MuteSpirit/CredsHolder/poc/ui-mpu-6050-with-oled-on-arduino-uno/Arduino-MPU_OLED_bb.jpg

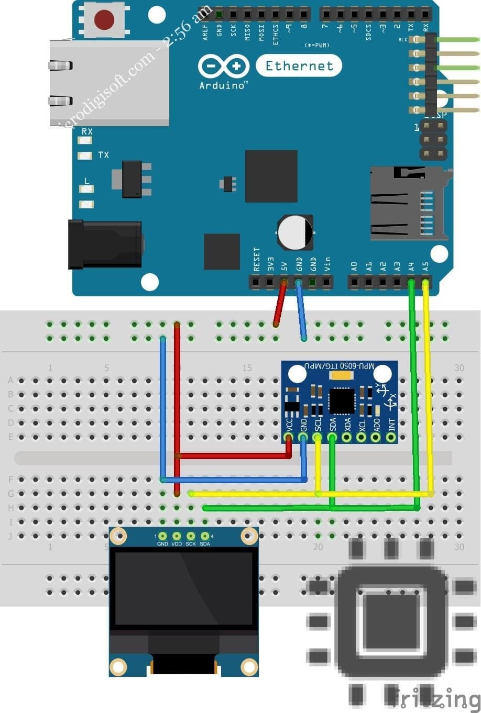
poc/ui-mpu-6050-with-oled-on-arduino-uno/Arduino-MPU_OLED_bb.jpg
