MuteSpirit/CredsHolder/proposals/creds-holder-navigation-option1-proposals-chevron-on-place.png

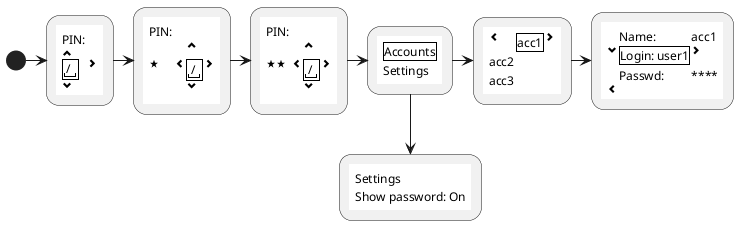
proposals/creds-holder-navigation-option1-proposals-chevron-on-place.png
