MuteSpirit/CredsHolder/src/device.cpp

// CredsHolder (Hardware Credential Manager)
// Copyright (C)  2026  Ivan Efimov aka MuteSpirit <mutespirit@yandex.ru>.
//
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
// You should have received a copy of the GNU General Public License
// along with this program.  If not, see <https://www.gnu.org/licenses/>.
#include "creds_holder.hpp"

#include <new>
#include <math.h>

#include <Arduino.h>

// Arduino Wire library is required if I2Cdev I2CDEV_ARDUINO_WIRE implementation
// is used in I2Cdev.h
#if I2CDEV_IMPLEMENTATION == I2CDEV_ARDUINO_WIRE
    #include "Wire.h"
#endif

// To be able handle MPU6050 events in time and avoid chip FIFO overloading
// it's needed to decrease speed of evetns generation to acceptable level
#define MPU6050_DMP_FIFO_RATE_DIVISOR 64 // work enough stable
// #define MPU6050_DMP_FIFO_RATE_DIVISOR 0x10 // ~ 60 Hz

#include "MPU6050/I2Cdev.h"
#include "MPU6050/MPU6050_6Axis_MotionApps20.h"
// TODO: try newer firmware from
// #include "MPU6050/MPU6050_6Axis_MotionApps612.h"
#include "MPU6050/MPU6050.h"

#include "device.hpp"

////////////////////////////////////////////////////////////////////////////////
enum class Movement : uint8_t
{
    clockwise,
    ccw, // counterclockwise
    none
};

struct SplashDetectCtx
{
    float ema {0.0f}; /// Exponential moving average

    /// like for keyboard we must detect when splash dissapear
    /// to react "not on button push but pull"
    uint8_t splashStarted {0};

    Movement mv {Movement::none};
};

class CredsHolderInputsImpl
{
public:
    CredsHolderInputsImpl(DeviceOutputs&);

public:
    DeviceOutputs& deviceOutputs_;

    BlindCall hooks_[static_cast<uint8_t>(DeviceInputs::UserAction::size)];

    MPU6050 mpu_;
    uint16_t packetSize_;    // expected DMP packet size (default is 42 bytes)
    uint8_t fifoBuffer_[64]; // FIFO storage buffer
                             //
    SplashDetectCtx pitchDetectCtx_;
    SplashDetectCtx rollDetectCtx_;
};

static volatile bool mpuInterrupt {false}; // indicates whether MPU interrupt pin has gone high
void dmpDataReady() {
    mpuInterrupt = true;
}

CredsHolderInputsImpl::CredsHolderInputsImpl(DeviceOutputs& deviceOutputs)
    : deviceOutputs_(deviceOutputs)
{
    for (size_t i = 0; i < static_cast<uint8_t>(DeviceInputs::UserAction::size); ++i) {
        hooks_[i] = BlindCall::stub();
    }
}

////////////////////////////////////////////////////////////////////////////////
CredsHolderInputs::CredsHolderInputs(DeviceOutputs& deviceOutputs)
{
    static_assert(sizeof(impl_) == sizeof(CredsHolderInputsImpl), "fix CredsHolderInputs::impl_ size");
    new(impl_) CredsHolderInputsImpl(deviceOutputs);
}

CredsHolderInputsImpl* CredsHolderInputs::impl()
{
    return reinterpret_cast<CredsHolderInputsImpl*>(impl_);
}

void
CredsHolderInputs::set(UserAction act, BlindCall cb)
{
    impl()->hooks_[static_cast<uint8_t>(act)] = cb;
}

void
CredsHolderInputs::unset(UserAction act)
{
    impl()->hooks_[static_cast<uint8_t>(act)] = BlindCall::stub();
}

bool
CredsHolderInputs::setup(void)
{
    // if (Serial) {Serial.println(F("CredsHolderInputs::setup 1"));}
#if I2CDEV_IMPLEMENTATION == I2CDEV_ARDUINO_WIRE
    Wire.begin();
    Wire.setClock(400000); // 400kHz I2C clock. Comment this line if having compilation difficulties
#elif I2CDEV_IMPLEMENTATION == I2CDEV_BUILTIN_FASTWIRE
    Fastwire::setup(400, true);
#endif

    MPU6050* mpu = &impl()->mpu_;

    mpu->initialize();

    // if (Serial) {Serial.println(F("CredsHolderInputs::setup 2"));}

    uint8_t devStatus = mpu->dmpInitialize(/* rate */ 20);
    if (devStatus != 0) {
        return false;
    }

    // if (Serial) {Serial.println(F("CredsHolderInputs::setup 3"));}

    // TODO: make initial calibration, store init values in internal memory and reuse when they are present
    // for my concrete MPU6050 module next offsets has been detected during calibration:
    mpu->setXAccelOffset(2508);
    mpu->setYAccelOffset(-2151);
    mpu->setZAccelOffset(992);

    mpu->setXGyroOffset(-147);
    mpu->setYGyroOffset(25);
    mpu->setZGyroOffset(68); 

    // Calibration Time: generate offsets and calibrate our MPU6050
    // mpu->CalibrateAccel(6);
    // mpu->CalibrateGyro(6);

    // if (Serial) {Serial.println(F("CredsHolderInputs::setup 4"));}

    // turn on the DMP, now that it's ready
    mpu->setDMPEnabled(true);

    // if (Serial) {Serial.println(F("CredsHolderInputs::setup 5"));}

    // enable Arduino interrupt detection
    attachInterrupt(digitalPinToInterrupt(MPU6050_CS_PIN), dmpDataReady, RISING);

    // TODO: add interrupts handling
    // uint8_t mpuIntStatus = mpu->getIntStatus();

    // set our DMP Ready flag so the main loop() function knows it's okay to use it

    // get expected DMP packet size for later comparison
    impl()->packetSize_ = mpu->dmpGetFIFOPacketSize();

    return true;
}

static bool isTiltHappen(SplashDetectCtx &ctx, const float p);

void
CredsHolderInputs::loop_step(void)
{
    // bool nothingToDo = true;
    //
    // noInterrupts();
    // if (mpuInterrupt) {
    //     mpuInterrupt = false;
    //     nothingToDo = false;
    // }
    // interrupts();
    //
    // if (nothingToDo) {
    //     return;
    // }

    if (!impl()->mpu_.dmpGetCurrentFIFOPacket(impl()->fifoBuffer_)) { // Get the Latest packet }
        // if (Serial) { Serial.println(impl()->mpu_.dmpGetFIFOPacketSize()); }
        return;
    }

    VectorFloat gravity;    // [x, y, z]            gravity vector
    Quaternion q;           // [w, x, y, z]         quaternion container
    float ypr[3];           // [yaw, pitch, roll]   yaw/pitch/roll container and gravity vector

    impl()->mpu_.dmpGetQuaternion(&q, impl()->fifoBuffer_);
    impl()->mpu_.dmpGetGravity(&gravity, &q);
    impl()->mpu_.dmpGetYawPitchRoll(ypr, &q, &gravity);

    if (Serial) {
        Serial.print(ypr[1] * 180 / M_PI); 
        Serial.print("; "); 
        Serial.print(ypr[2] * 180 / M_PI); 
        Serial.println(); 
    }

    uint8_t splashStarted = impl()->pitchDetectCtx_.splashStarted;
    if (isTiltHappen(impl()->pitchDetectCtx_, ypr[1] * 180 / M_PI)) {
        if (impl()->pitchDetectCtx_.mv == Movement::clockwise) {
            if (Serial) {Serial.println(F("UserAction::up"));}
            impl()->hooks_[static_cast<uint8_t>(UserAction::up)]();
        } else {
            if (Serial) {Serial.println(F("UserAction::down"));}
            impl()->hooks_[static_cast<uint8_t>(UserAction::down)]();
        }
    } else {
        if (0 == splashStarted && impl()->pitchDetectCtx_.splashStarted > 0) {
            // enough big tilt angle has been detected
            impl()->deviceOutputs_.notify(DeviceOutputs::Feedback::halfTilt);
        } 
    }

    splashStarted = impl()->rollDetectCtx_.splashStarted;
    if (isTiltHappen(impl()->rollDetectCtx_, ypr[2] * 180 / M_PI)) {
        if (impl()->rollDetectCtx_.mv == Movement::clockwise) {
            if (Serial) {Serial.println(F("UserAction::left"));}
            impl()->hooks_[static_cast<uint8_t>(UserAction::left)]();
        } else {
            if (Serial) {Serial.println(F("UserAction::right"));}
            impl()->hooks_[static_cast<uint8_t>(UserAction::right)]();
        }
    } else {
        if (0 == splashStarted && impl()->rollDetectCtx_.splashStarted > 0) {
            // enough big tilt angle has been detected
            impl()->deviceOutputs_.notify(DeviceOutputs::Feedback::halfTilt);
        } 
    }

}

////////////////////////////////////////////////////////////////////////////////
static
bool
isTiltHappen(SplashDetectCtx &ctx, const float p)
{
  constexpr float threshold = 7; // usually tilt angle is about 15 degrees
  constexpr float alpha = 0.15;

  ctx.ema = alpha * p + (1.0 - alpha) * ctx.ema;

  float delta = p - ctx.ema;

  if (abs(delta) >= threshold) {
    ++ctx.splashStarted;
    // FIXME: we may quickly tilt device up and down and "mv" will
    // be updated to the latest tilt accordingly
    ctx.mv = (delta >= 0) ? Movement::clockwise : Movement::ccw;

    if (ctx.splashStarted >= 3) {
      // MPU-6050 DMP is configured to measure 1 time per second
      // so if we see that splash is happening 3 second in a raw
      // then it's just a new position of device
      // TODO: decide how detect "long tilt"
      ctx.splashStarted = 0;
      ctx.mv = Movement::none;
    }
    return false;
  } else {
    if (ctx.splashStarted > 0) {
      // we return device back to original position
      // so tilt finished and device may start a reaction
      ctx.splashStarted = 0;
      return true;
    } else {
      ctx.mv = Movement::none;
      return false;
    }
  }
}

////////////////////////////////////////////////////////////////////////////////
CredsHolderOutputs::CredsHolderOutputs(const uint8_t vibroMotorPin)
: vibroMotorPin_(vibroMotorPin)
{}

bool
CredsHolderOutputs::setup(void)
{
    pinMode(vibroMotorPin_, OUTPUT);
    digitalWrite(vibroMotorPin_, LOW); // to avoid active vibration at device boot time
    return true;
}

void
CredsHolderOutputs::loop_step(void)
{}


void
CredsHolderOutputs::notify(Feedback fb)
{
    switch (fb) {
        case Feedback::halfTilt:
            digitalWrite(vibroMotorPin_, HIGH);
            delay(shortBipDelayMs);
            digitalWrite(vibroMotorPin_, LOW);
            break;

        default:
            break;
    }
}
