MuteSpirit/CredsHolder/src/device.hpp

// CredsHolder (Hardware Credential Manager)
// Copyright (C)  2026  Ivan Efimov aka MuteSpirit <mutespirit@yandex.ru>.
//
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
// You should have received a copy of the GNU General Public License
// along with this program.  If not, see <https://www.gnu.org/licenses/>.
#pragma once

#include "creds_holder.hpp"
#include <Arduino.h>

#include "device_inputs.hpp"
#include "device_outputs.hpp"

#if defined(ARDUINO_ARCH_AVR) // Arduino

// OLED Display
#define OLED_SDA_PIN    2
#define OLED_SCK_PIN    3
#define OLED_I2C_ADDR   0x3C

#define MPU6050_CS_PIN  D5

#define VIBRO_MOTOR_IN_PIN  D10

#elif defined(ARDUINO_ARCH_NRF52) // Pro Micro nRF52840

// OLED Display
#define OLED_SDA_PIN    D6
#define OLED_SCK_PIN    D7
#define OLED_I2C_ADDR   0x3C

#define MPU6050_CS_PIN  D5

#define VIBRO_MOTOR_IN_PIN  D10

#elif defined(EPOXY_DUINO) // Unit tests

// OLED Display
#define OLED_SDA_PIN    D6
#define OLED_SCK_PIN    D7
#define OLED_I2C_ADDR   0x3C

#define MPU6050_CS_PIN  D5

#define VIBRO_MOTOR_IN_PIN  D10

#else
#error("Unknown board type")
#endif // defined(ARDUINO_ARCH_AVR)

class CredsHolderInputsImpl;

////////////////////////////////////////////////////////////////////////////////
class CredsHolderInputs : public DeviceInputs
{
public:
    CredsHolderInputs(DeviceOutputs&);

    virtual void set(UserAction act, BlindCall cb) override;
    virtual void unset(UserAction act) override;

    /// @return "true" if Ok and "false" if initializing fail and device cannot be used, init reboot in that case.
    virtual bool setup(void) override;

    virtual void loop_step(void) override;

protected:
    CredsHolderInputsImpl* impl();

protected:
    uint8_t impl_[296]; /// "insulation' for internal data
};

////////////////////////////////////////////////////////////////////////////////
class CredsHolderOutputs : public DeviceOutputs
{
public:
    CredsHolderOutputs(const uint8_t vibroMotorPin = VIBRO_MOTOR_IN_PIN);

    virtual void notify(Feedback) override;

    virtual bool setup(void) override;
    virtual void loop_step(void) override;

protected:
    uint8_t vibroMotorPin_;
    constexpr static const size_t shortBipDelayMs = 175; // ms
};
