MuteSpirit/CredsHolder/src/accounts_menu.t.cpp

// CredsHolder (Hardware Credential Manager)
// Copyright (C)  2026  Ivan Efimov aka MuteSpirit <mutespirit@yandex.ru>.
//
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
// You should have received a copy of the GNU General Public License
// along with this program.  If not, see <https://www.gnu.org/licenses/>.
#if defined(EPOXY_DUINO)

#include "accounts_menu.hpp"

#include <array>

#include "device_inputs.hpp"
#include "settings.hpp"
#include "memory_block_storage.hpp"

#include "model/account.hpp"
#include "model/storage.hpp"

#include "t/in_memory_oled.hpp"
#include "t/imitated_user_unputs.hpp"

// Must be included as the last one to avoid troubles with macro "test"
// when such word is used in headers above
#include <AUnitVerbose.h>

class AccountsMenuTest : public aunit::TestOnce
{
public:
    virtual void setup() override
    {
        TestOnce::setup();

        memset(buf, 0, sz);
    }

protected:
    OledInMem<16, 4> oled_;
    ImitatedUserInputs userInputs_;
    MemoryBlockStorage<1024, 64> bs_;
    ModelStorage<Account> ms_ {bs_};

    constexpr static uint8_t sz = 16;
    char buf[sz];
};

testF(AccountsMenuTest, ctor)
{
    AccountsMenu menu(oled_, userInputs_, ms_);
};

testF(AccountsMenuTest, draw_empty_account_storage)
{
    AccountsMenu menu(oled_, userInputs_, ms_);

    menu.draw();

    oled_.getLine(0, buf, sz); assertStringCaseEqual("Accounts", buf);
    oled_.getLine(1, buf, sz); assertStringCaseEqual("", buf);
    oled_.getLine(2, buf, sz); assertStringCaseEqual("", buf);
    oled_.getLine(3, buf, sz); assertStringCaseEqual("", buf);
}

testF(AccountsMenuTest, draw_single_account)
{
    Account acc {"acc0", "login", "passwd"};
    assertTrue(ms_.add(acc));

    AccountsMenu menu(oled_, userInputs_, ms_);

    menu.draw();

    oled_.getLine(0, buf, sz); assertStringCaseEqual("Accounts", buf);
    oled_.getLine(1, buf, sz); assertStringCaseEqual("acc0", buf);
    oled_.getLine(2, buf, sz); assertStringCaseEqual("", buf);
    oled_.getLine(3, buf, sz); assertStringCaseEqual("", buf);
}

testF(AccountsMenuTest, draw_the_same_accounts_as_visible)
{
    std::array<Account, 3> aa {{
        {"acc0", "login0", "passwd0"},
        {"acc1", "login1", "passwd1"},
        {"acc2", "login2", "passwd2"},
    }};

    for (auto acc : aa) {
        assertTrue(ms_.add(acc));
    }

    AccountsMenu menu(oled_, userInputs_, ms_);

    assertTrue(aa[0] == menu.selected());

    oled_.clear();
    menu.draw();

    memset(buf, 0, sz);
    oled_.getLine(0, buf, sz); assertStringCaseEqual("Accounts", buf);
    oled_.getLine(1, buf, sz); assertStringCaseEqual("acc0", buf);
    oled_.getLine(2, buf, sz); assertStringCaseEqual("acc1", buf);
    oled_.getLine(3, buf, sz); assertStringCaseEqual("acc2", buf);

    menu.activate();

    userInputs_.tilt(DeviceInputs::UserAction::down); // acc0 ->acc1
    assertTrue(aa[1] == menu.selected());

    userInputs_.tilt(DeviceInputs::UserAction::down); // acc1 ->acc2
    assertTrue(aa[2] == menu.selected());

    userInputs_.tilt(DeviceInputs::UserAction::down); // acc2 ->acc0
    assertTrue(aa[0] == menu.selected());

    oled_.clear();
    menu.draw();

    memset(buf, 0, sz);
    oled_.getLine(0, buf, sz); assertStringCaseEqual("Accounts", buf);
    oled_.getLine(1, buf, sz); assertStringCaseEqual("acc0", buf);
    oled_.getLine(2, buf, sz); assertStringCaseEqual("acc1", buf);
    oled_.getLine(3, buf, sz); assertStringCaseEqual("acc2", buf);
}

testF(AccountsMenuTest, draw_more_accounts_then_visible)
{
    std::array<Account, 4> aa {{
        {"acc0", "login0", "passwd0"},
        {"acc1", "login1", "passwd1"},
        {"acc2", "login2", "passwd2"},
        {"acc3", "login3", "passwd3"}
    }};

    for (auto acc : aa) {
        assertTrue(ms_.add(acc));
    }

    AccountsMenu menu(oled_, userInputs_, ms_);
    menu.activate();

    assertTrue(aa[0] == menu.selected());
    menu.draw();

    oled_.getLine(0, buf, sz); assertStringCaseEqual("Accounts", buf);
    oled_.getLine(1, buf, sz); assertStringCaseEqual("acc0", buf);
    oled_.getLine(2, buf, sz); assertStringCaseEqual("acc1", buf);
    oled_.getLine(3, buf, sz); assertStringCaseEqual("acc2", buf);

    userInputs_.tilt(DeviceInputs::UserAction::down); // acc0 ->acc1
    assertTrue(aa[1] == menu.selected());

    userInputs_.tilt(DeviceInputs::UserAction::down); // acc1 ->acc2
    assertTrue(aa[2] == menu.selected());

    userInputs_.tilt(DeviceInputs::UserAction::down); // acc2 ->acc3
    assertTrue(aa[3] == menu.selected());

    menu.draw();

    memset(buf, 0, sz);
    oled_.getLine(0, buf, sz); assertStringCaseEqual("Accounts", buf);
    oled_.getLine(1, buf, sz); assertStringCaseEqual("acc1", buf);
    oled_.getLine(2, buf, sz); assertStringCaseEqual("acc2", buf);
    oled_.getLine(3, buf, sz); assertStringCaseEqual("acc3", buf);
}

#endif // defined(EPOXY_DUINO)
