MuteSpirit/CredsHolder/src/memory_block_storage.hpp

// CredsHolder (Hardware Credential Manager)
// Copyright (C)  2026  Ivan Efimov aka MuteSpirit <mutespirit@yandex.ru>.
//
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
// You should have received a copy of the GNU General Public License
// along with this program.  If not, see <https://www.gnu.org/licenses/>.
#pragma once

#include <string.h>
#include "block_storage.hpp"


class MemoryBlockStorageTestHelper;

template<size_t fullSizeBytes, size_t pageSizeBytes>
class MemoryBlockStorage : public BlockStorage
{
public:
    virtual size_t minAddr() const override;
    virtual size_t maxAddr() const override;

    virtual bool isAddrOk(const size_t addr) const override;

    virtual uint8_t read(const size_t addr) override;
    virtual void write(const size_t addr, const uint8_t b) override;

    virtual void read(const size_t addr, uint8_t *buf, const size_t size) override;
    virtual void write(const size_t addr, const uint8_t *buf, const size_t size) override;

    virtual void factoryReset() override;

    MemoryBlockStorage();

protected:
    uint8_t getResetFlag();
    void setResetFlag();

protected:
    uint8_t store_[fullSizeBytes];
    uint32_t offset_{0};

    friend MemoryBlockStorageTestHelper;
};

#define RESET_FLAG (0xff)

template<size_t fullSizeBytes, size_t pageSizeBytes>
size_t
MemoryBlockStorage<fullSizeBytes, pageSizeBytes>::minAddr() const
{
    return 0;
}

template<size_t fullSizeBytes, size_t pageSizeBytes>
size_t
MemoryBlockStorage<fullSizeBytes, pageSizeBytes>::maxAddr() const
{
    return fullSizeBytes - 1 /* init flag size */;
}

template<size_t fullSizeBytes, size_t pageSizeBytes>
bool
MemoryBlockStorage<fullSizeBytes, pageSizeBytes>::isAddrOk(const size_t addr) const
{
    return minAddr() <= addr && addr < maxAddr();
}

template<size_t fullSizeBytes, size_t pageSizeBytes>
MemoryBlockStorage<fullSizeBytes, pageSizeBytes>::MemoryBlockStorage()
    : store_{0}
{
    setResetFlag();
}

template<size_t fullSizeBytes, size_t pageSizeBytes>
uint8_t
MemoryBlockStorage<fullSizeBytes, pageSizeBytes>::getResetFlag()
{
    return read(fullSizeBytes - 1);
}

template<size_t fullSizeBytes, size_t pageSizeBytes>
void
MemoryBlockStorage<fullSizeBytes, pageSizeBytes>::setResetFlag()
{
    store_[fullSizeBytes - 1] = RESET_FLAG;
}

template<size_t fullSizeBytes, size_t pageSizeBytes>
uint8_t
MemoryBlockStorage<fullSizeBytes, pageSizeBytes>::read(const size_t addr) 
{
    return store_[addr];
}

template<size_t fullSizeBytes, size_t pageSizeBytes>
void
MemoryBlockStorage<fullSizeBytes, pageSizeBytes>::write(const size_t addr, const uint8_t b) 
{
    if (addr >= fullSizeBytes - 1) {
        return;
    }
    store_[addr] = b;
}

template<size_t fullSizeBytes, size_t pageSizeBytes>
void
MemoryBlockStorage<fullSizeBytes, pageSizeBytes>::read(const size_t addr, uint8_t *buf, const size_t size) 
{
    for (uint32_t i = addr, j = 0; i < addr + size && i < fullSizeBytes; ++i, ++j) {
        buf[j] = read(i);
    }
}

template<size_t fullSizeBytes, size_t pageSizeBytes>
void
MemoryBlockStorage<fullSizeBytes, pageSizeBytes>::write(const size_t addr, const uint8_t *buf, const size_t size) 
{
    for (uint32_t i = addr, j = 0; j < size && i < fullSizeBytes; ++j, ++i) {
        write(i, buf[j]);
    }
}

template<size_t fullSizeBytes, size_t pageSizeBytes>
void
MemoryBlockStorage<fullSizeBytes, pageSizeBytes>::factoryReset()
{
    memset(store_, 0, fullSizeBytes);
    setResetFlag();
}
